ieiao/epd-clock/fw/clock/drivers/gpio.c

#include <msp430g2553.h>
#include "gpio.h"
#include "pm.h"
#include "core.h"

void gpio_init(void)
{
    /* 
     * P1.0 ADC 复用配置不关心
     * P1.6 = SCL
     * P1.7 = SDA
     * 其余IO无复用
     */
    P1SEL = BIT1 + BIT2 + BIT6 + BIT7;
    P1SEL2 = BIT1 + BIT2 + BIT6 + BIT7;

    /* 
     * P1.3 = FLASHCS           O
     * P1.4 = AIN_C             O
     * P1.5 = RTC_WAKE          I
     * 初始化状态
     */
    P1DIR = BIT3 + BIT4;
    P1OUT = BIT3 + BIT4;

    /* 使能RTC唤醒引脚中断，清除中断状态 */
    P1IES |= BIT5;
    P1IFG &= ~BIT5;
    P1IE |= BIT5;

    /*
     * P3.0 = MISO              I
     * P3.1 = EPD_BUSY          I
     * P3.2 = CLK               O
     * P3.3 = EPD_PWR_EN#       O
     * P3.4 = MOSI              O
     * P3.5 = EPD_RST#          O
     * P3.6 = EPD_DC#           O
     * P3.7 = EPC_CS#           O
     */
    P3DIR = BIT2 + BIT3 + BIT4 + BIT5 + BIT6 + BIT7;

    /*
     * EPC_CS      = 1
     * PED_PWR_CTL = 1
     * SPI_CLK     = 0 (SPI MODE 0 IDLE status)
     */
    P3OUT = BIT3 + BIT5 + BIT7;

    /* 
     * P2 ALL input
     */
    P2IES |= BIT0 + BIT1 + BIT2;
    P2IFG &= ~(BIT0 + BIT1 + BIT2);
}

void gpio_resume(void)
{
    gpio_init();
}

// Port 1 interrupt service routine
#if defined(__TI_COMPILER_VERSION__) || defined(__IAR_SYSTEMS_ICC__)
#pragma vector=PORT1_VECTOR
__interrupt void Port_1(void)
#elif defined(__GNUC__)
void __attribute__ ((interrupt(PORT1_VECTOR))) Port_1 (void)
#else
#error Compiler not supported!
#endif
{
    P1IFG &= ~BIT5;
    set_wakeup_type(WAKEUP_BY_RTC);
    SYS_EXIT_SLEEP;
}

// Port 2 interrupt service routine
#if defined(__TI_COMPILER_VERSION__) || defined(__IAR_SYSTEMS_ICC__)
#pragma vector=PORT2_VECTOR
__interrupt void Port_2(void)
#elif defined(__GNUC__)
void __attribute__ ((interrupt(PORT2_VECTOR))) Port_2 (void)
#else
#error Compiler not supported!
#endif
{
    P2IFG &= ~(BIT0 + BIT1 + BIT2);
    P2IE &= ~(BIT0 + BIT1 + BIT2);
    set_wakeup_type(WAKEUP_BY_BUTTON);
    SYS_EXIT_SLEEP;
}
